EmilAltmann/Buzzerino/images/buzzerino_pcb_back.jpg

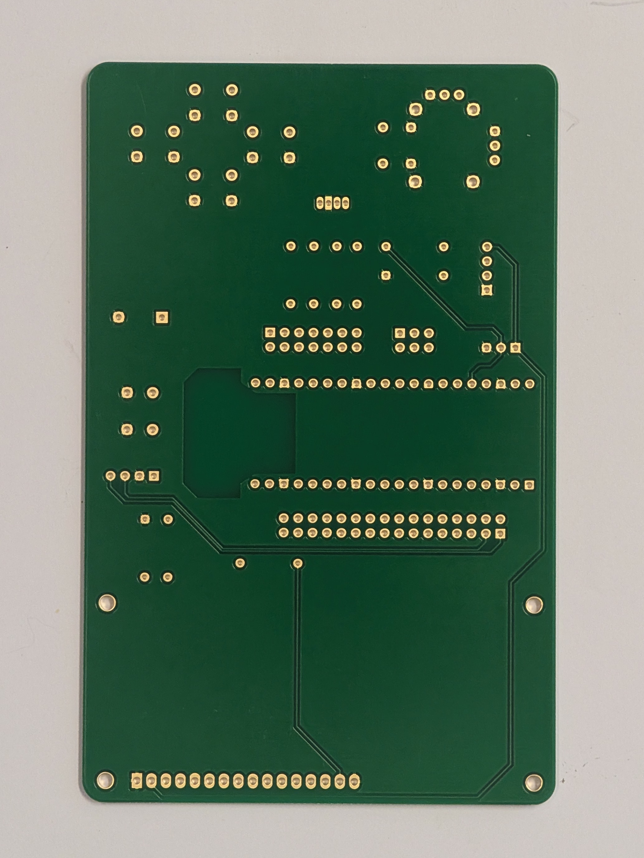
images/buzzerino_pcb_back.jpg
