EmilAltmann/Buzzerino/images/buzzerino_pcb_front.jpg

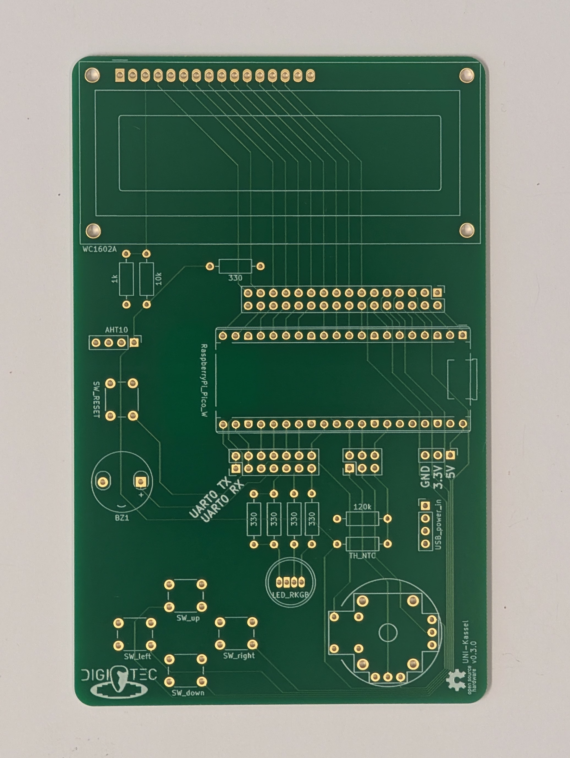
images/buzzerino_pcb_front.jpg
