EmilAltmann/Buzzerino/example_programs/rpi_program_selector/lcd1602.c

#include "lcd1602.h"
#include "pico/stdlib.h"
#include "hardware/gpio.h"

#define LCD_D7 6
#define LCD_D6 7
#define LCD_D5 8
#define LCD_D4 9
#define LCD_D3 10
#define LCD_D2 11
#define LCD_D1 12
#define LCD_D0 13

#define LCD_E  14
#define LCD_RS 15

static uint8_t _disp_ctrl = 0x0C; // Display on, cursor off, blink off

static void lcd_pulse_e(void)
{
    gpio_put(LCD_E, 1);
    sleep_us(1);
    gpio_put(LCD_E, 0);
}

static void lcd_write8(uint8_t val)
{
    gpio_put(LCD_D0, (val >> 0) & 1);
    gpio_put(LCD_D1, (val >> 1) & 1);
    gpio_put(LCD_D2, (val >> 2) & 1);
    gpio_put(LCD_D3, (val >> 3) & 1);
    gpio_put(LCD_D4, (val >> 4) & 1);
    gpio_put(LCD_D5, (val >> 5) & 1);
    gpio_put(LCD_D6, (val >> 6) & 1);
    gpio_put(LCD_D7, (val >> 7) & 1);

    lcd_pulse_e();
}

static void lcd_cmd(uint8_t cmd)
{
    gpio_put(LCD_RS, 0);
    lcd_write8(cmd);

    if (cmd == 0x01 || cmd == 0x02)
        sleep_ms(2);
    else
        sleep_us(50);
}

static void lcd_data(uint8_t data)
{
    gpio_put(LCD_RS, 1);
    lcd_write8(data);
    sleep_us(50);
}

void lcd_init(void)
{
    const uint lcd_pins[] = {
        LCD_D0, LCD_D1, LCD_D2, LCD_D3,
        LCD_D4, LCD_D5, LCD_D6, LCD_D7,
        LCD_E, LCD_RS
    };

    for (uint i = 0; i < sizeof(lcd_pins) / sizeof(lcd_pins[0]); i++)
    {
        gpio_init(lcd_pins[i]);
        gpio_set_dir(lcd_pins[i], GPIO_OUT);
        gpio_put(lcd_pins[i], 0);
    }

    sleep_ms(20);

    lcd_cmd(0x38);       // 8-bit, 2 lines, 5x8 font
    lcd_cmd(0x08);       // display off
    lcd_cmd(0x01);       // clear display
    lcd_cmd(0x06);       // entry mode: increment, no shift
    lcd_cmd(_disp_ctrl); // display on
}

void lcd_clear(void)
{
    lcd_cmd(0x01);
}

void lcd_home(void)
{
    lcd_cmd(0x02);
}

void lcd_putc(char c)
{
    lcd_data((uint8_t)c);
}

void lcd_puts(const char *s)
{
    while (*s)
        lcd_putc(*s++);
}

void lcd_gotoxy(uint8_t row, uint8_t col)
{
    static const uint8_t row_addr[2] = {0x00, 0x40};
    lcd_cmd(0x80 | (row_addr[row & 1] + (col & 0x0F)));
}

void lcd_cursor_visible(uint8_t on)
{
    if (on)
        _disp_ctrl |= 0x02;
    else
        _disp_ctrl &= ~0x02;

    lcd_cmd(_disp_ctrl);
}

void lcd_cursor_blink(uint8_t on)
{
    if (on)
        _disp_ctrl |= 0x01;
    else
        _disp_ctrl &= ~0x01;

    lcd_cmd(_disp_ctrl);
}

void lcd_cursor_left(void)
{
    lcd_cmd(0x10);
}

void lcd_cursor_right(void)
{
    lcd_cmd(0x14);
}

void lcd_create_char(uint8_t slot, const uint8_t bitmap[8])
{
    slot &= 0x07;                 // only 0..7 allowed
    lcd_cmd(0x40 | (slot << 3));  // set CGRAM address

    for (int i = 0; i < 8; i++)
        lcd_data(bitmap[i] & 0x1F);

    lcd_cmd(0x80); // back to DDRAM
}
